us3r-d0e5nt-3x1st/esp32c5-airunit-nano/photos/1.png

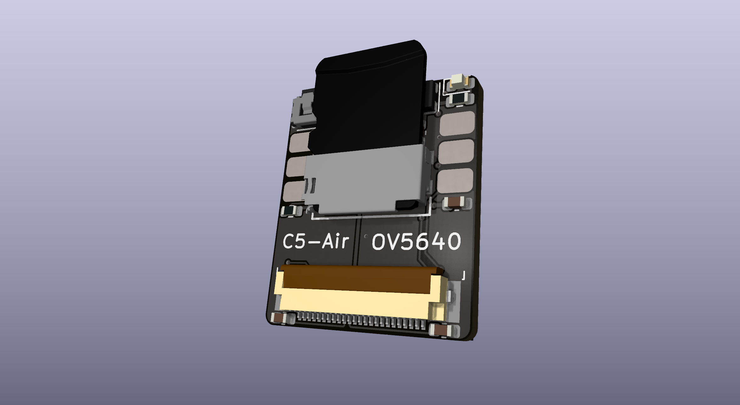
photos/1.png
