us3r-d0e5nt-3x1st/esp32c5-airunit-nano/photos/2.png

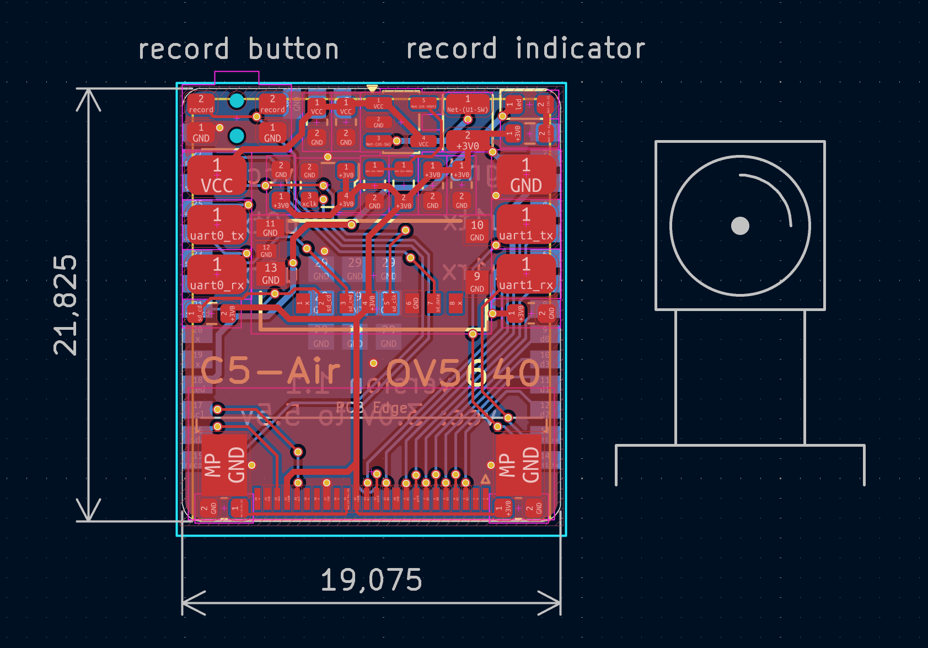
photos/2.png
